ThKattanek/reflow_ofen_umbau_kit/firmware/kty84-130_teperature_table.h

// ADC Values: 156 - 581 (-40° - 300°)
const int16_t temperature_table[426] PROGMEM =
{
    -40,-39,-38,-37,-36,-35,-35,-34,-33,-32,-31,
    -30,-29,-28,-28,-27,-26,-25,-24,-23,-23,-22,-21,
    -20,-19,-18,-18,-17,-16,-15,-14,-13,-13,-12,-11,
    -10,-9,-8,-8,-7,-6,-5,-5,-4,-3,-2,-2,-1,
    0,1,2,2,3,4,5,5,6,7,8,8,9,
    10,11,11,12,13,14,14,15,16,16,17,18,19,19,
    20,21,22,23,23,24,
    25,26,26,27,28,29,29,
    30,31,31,32,33,34,34,35,36,36,37,38,39,39,
    40,41,41,42,43,44,44,45,46,46,47,48,49,49,
    50,51,52,52,53,54,55,55,56,57,58,58,59,
    60,61,61,62,63,64,64,65,66,66,67,68,69,69,
    70,71,71,72,73,74,74,75,76,76,77,78,79,79,
    80,81,81,82,83,84,84,85,86,86,87,88,89,89,
    90,91,91,92,93,94,94,95,96,96,97,98,99,99,
    100,101,101,102,103,104,104,105,106,106,107,108,109,109,
    110,111,111,112,113,114,114,115,116,116,117,118,119,119,
    120,121,121,122,123,124,124,125,126,126,127,128,129,129,
    130,131,132,132,133,134,135,135,136,137,138,138,139,
    140,141,141,142,143,144,144,145,146,146,147,148,149,149,
    150,151,152,152,153,154,155,155,156,157,158,158,159,
    160,161,162,162,163,164,165,165,166,167,168,168,169,
    170,171,172,172,173,174,175,175,176,177,178,178,179,
    180,181,182,183,183,184,185,186,187,188,188,189,
    190,191,192,192,193,194,195,195,196,197,198,198,199,
    200,201,202,203,203,204,205,206,207,208,208,209,
    210,211,212,213,213,214,215,216,217,218,218,219,
    220,221,222,223,223,224,225,226,227,228,228,229,
    230,231,232,233,234,235,235,236,237,238,239,
    240,241,242,243,244,245,245,246,247,248,249,
    250,251,252,253,254,255,255,256,257,258,259,
    260,261,262,263,264,265,265,266,267,268,269,
    270,271,272,273,274,275,276,277,278,279,
    280,281,282,283,284,286,287,288,289,
    290,291,293,294,295,296,298,299,300
};
